milenko-s/LC-2301/documentation/pictures/IMG_1649.JPG

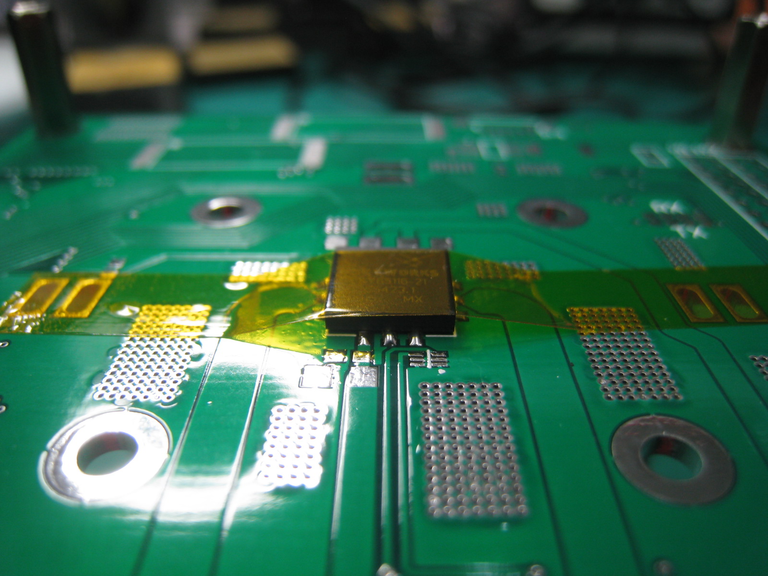
documentation/pictures/IMG_1649.JPG
