milenko-s/LC-2301/documentation/pictures/IMG_3462.JPG

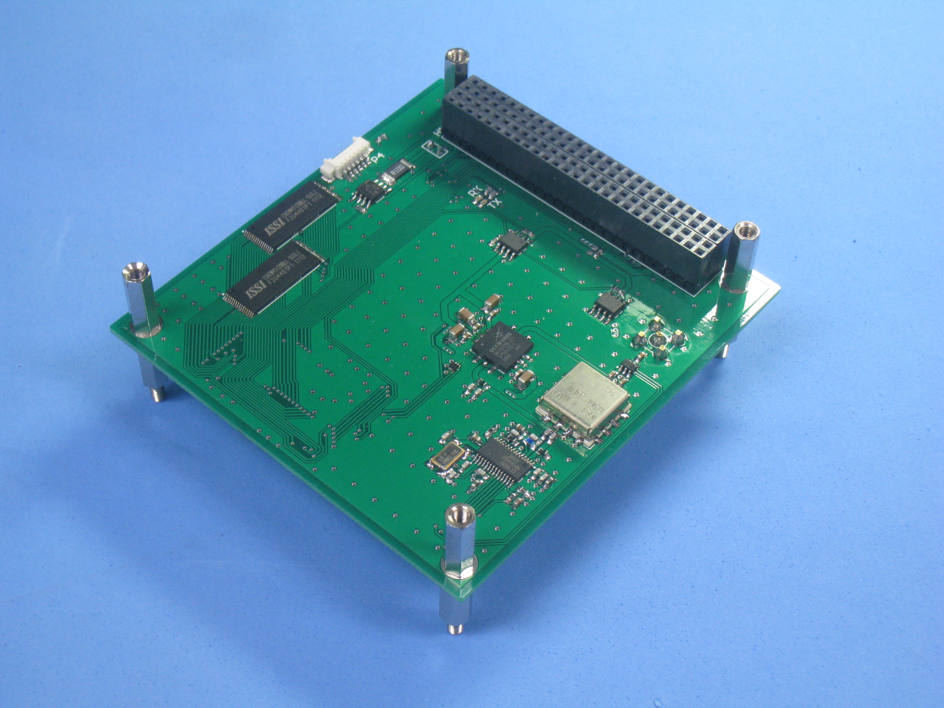
documentation/pictures/IMG_3462.JPG
