milenko-s/LC-2301/documentation/pictures/IMG_3463.JPG

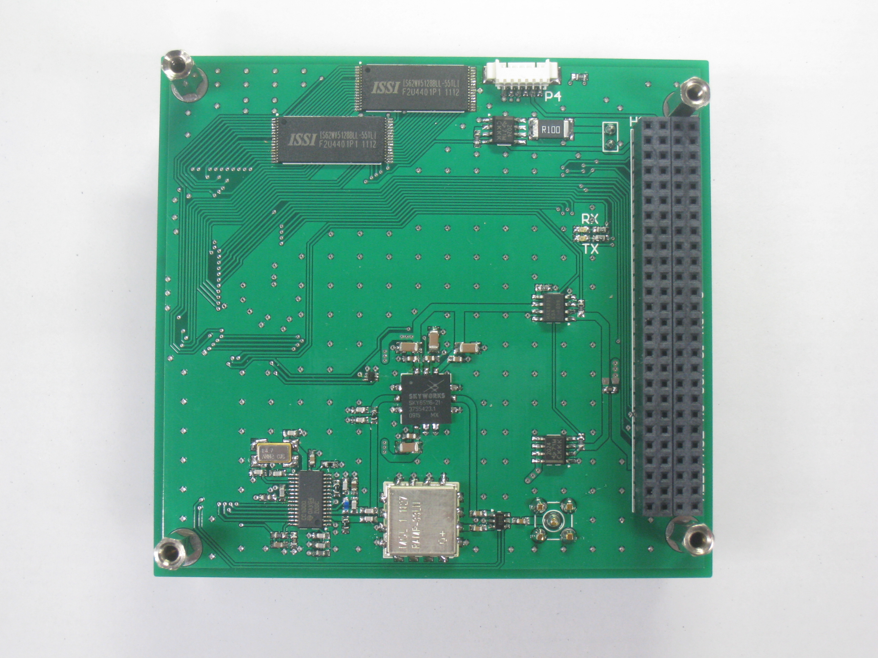
documentation/pictures/IMG_3463.JPG
