milenko-s/LC-2301/documentation/pictures/IMG_3464.JPG

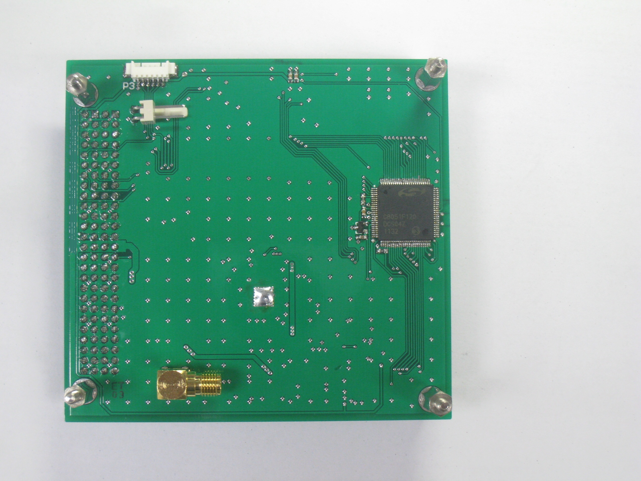
documentation/pictures/IMG_3464.JPG
